maxrangner/nasta/components/display/matrix_animations.h

#pragma once

#include <stdint.h>

inline constexpr uint8_t kBoot1[64] = {
    1,0,0,0,0,0,0,0,
    0,0,0,0,0,0,0,0,
    0,0,0,0,0,0,0,0,
    0,0,0,0,0,0,0,0,
    0,0,0,0,0,0,0,0,
    0,0,0,0,0,0,0,0,
    0,0,0,0,0,0,0,0,
    0,0,0,0,0,0,0,0
};

inline constexpr uint8_t kBoot2[64] = {
    0,1,0,0,0,0,0,0,
    0,0,0,0,0,0,0,0,
    0,0,0,0,0,0,0,0,
    0,0,0,0,0,0,0,0,
    0,0,0,0,0,0,0,0,
    0,0,0,0,0,0,0,0,
    0,0,0,0,0,0,0,0,
    0,0,0,0,0,0,0,0
};

inline constexpr uint8_t kBoot3[64] = {
    0,0,1,0,0,0,0,0,
    0,0,0,0,0,0,0,0,
    0,0,0,0,0,0,0,0,
    0,0,0,0,0,0,0,0,
    0,0,0,0,0,0,0,0,
    0,0,0,0,0,0,0,0,
    0,0,0,0,0,0,0,0,
    0,0,0,0,0,0,0,0
};

inline constexpr uint8_t kBoot4[64] = {
    0,0,0,1,0,0,0,0,
    0,0,0,0,0,0,0,0,
    0,0,0,0,0,0,0,0,
    0,0,0,0,0,0,0,0,
    0,0,0,0,0,0,0,0,
    0,0,0,0,0,0,0,0,
    0,0,0,0,0,0,0,0,
    0,0,0,0,0,0,0,0
};

inline constexpr uint8_t kBoot5[64] = {
    0,0,0,0,1,0,0,0,
    0,0,0,0,0,0,0,0,
    0,0,0,0,0,0,0,0,
    0,0,0,0,0,0,0,0,
    0,0,0,0,0,0,0,0,
    0,0,0,0,0,0,0,0,
    0,0,0,0,0,0,0,0,
    0,0,0,0,0,0,0,0
};

inline constexpr uint8_t kBoot6[64] = {
    0,0,0,0,0,1,0,0,
    0,0,0,0,0,0,0,0,
    0,0,0,0,0,0,0,0,
    0,0,0,0,0,0,0,0,
    0,0,0,0,0,0,0,0,
    0,0,0,0,0,0,0,0,
    0,0,0,0,0,0,0,0,
    0,0,0,0,0,0,0,0
};

inline constexpr uint8_t kBoot7[64] = {
    0,0,0,0,0,0,1,0,
    0,0,0,0,0,0,0,0,
    0,0,0,0,0,0,0,0,
    0,0,0,0,0,0,0,0,
    0,0,0,0,0,0,0,0,
    0,0,0,0,0,0,0,0,
    0,0,0,0,0,0,0,0,
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
    kBoot61, kBoot62, kBoot63, kBoot64, kBoot65, kBoot66,
    kBoot67, kBoot68, kBoot69, kBoot70, kBoot71
};

inline constexpr const uint8_t* kWorkAnimation[] = {
    kWork1, kWork2, kWork3, kWork4
};

inline constexpr const uint8_t* kHeartAnimation[] = {
    kHeart1, kHeart2
};
