maxrangner/nasta/components/display/matrix_graphics.h

#pragma once

#include <stdint.h>

inline constexpr uint8_t kHeart[64] = {
    0,0,0,0,0,0,0,0,
    0,1,1,0,0,1,1,0,
    1,0,0,1,1,0,0,1,
    1,0,0,0,0,0,0,1,
    0,1,0,0,0,0,1,0,
    0,0,1,0,0,1,0,0,
    0,0,0,1,1,0,0,0,
    0,0,0,0,0,0,0,0
};

inline constexpr uint8_t kNum0[64] = {
    0,0,0,0,0,0,0,0,
    0,0,0,1,1,0,0,0,
    0,0,1,0,0,1,0,0,
    0,0,1,0,0,1,0,0,
    0,0,1,0,0,1,0,0,
    0,0,1,0,0,1,0,0,
    0,0,0,1,1,0,0,0,
    0,0,0,0,0,0,0,0
};

inline constexpr uint8_t kNum1[64] = {
    0,0,0,0,0,0,0,0,
    0,0,0,0,1,0,0,0,
    0,0,0,1,1,0,0,0,
    0,0,0,0,1,0,0,0,
    0,0,0,0,1,0,0,0,
    0,0,0,0,1,0,0,0,
    0,0,0,1,1,1,0,0,
    0,0,0,0,0,0,0,0
};

inline constexpr uint8_t kNum2[64] = {
    0,0,0,0,0,0,0,0,
    0,0,0,1,1,0,0,0,
    0,0,1,0,0,1,0,0,
    0,0,0,0,1,0,0,0,
    0,0,0,1,0,0,0,0,
    0,0,1,0,0,0,0,0,
    0,0,1,1,1,1,0,0,
    0,0,0,0,0,0,0,0
};

inline constexpr uint8_t kNum3[64] = {
    0,0,0,0,0,0,0,0,
    0,0,0,1,1,0,0,0,
    0,0,1,0,0,1,0,0,
    0,0,0,0,1,0,0,0,
    0,0,0,0,0,1,0,0,
    0,0,1,0,0,1,0,0,
    0,0,0,1,1,0,0,0,
    0,0,0,0,0,0,0,0
};

inline constexpr uint8_t kNum4[64] = {
    0,0,0,0,0,0,0,0,
    0,0,0,0,0,1,0,0,
    0,0,0,0,1,1,0,0,
    0,0,0,1,0,1,0,0,
    0,0,1,0,0,1,0,0,
    0,0,1,1,1,1,0,0,
    0,0,0,0,0,1,0,0,
    0,0,0,0,0,0,0,0
};

inline constexpr uint8_t kNum5[64] = {
    0,0,0,0,0,0,0,0,
    0,0,1,1,1,1,0,0,
    0,0,1,0,0,0,0,0,
    0,0,1,1,1,0,0,0,
    0,0,0,0,0,1,0,0,
    0,0,0,0,0,1,0,0,
    0,0,1,1,1,0,0,0,
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
    kNum0, kNum1, kNum2, kNum3, kNum4, kNum5, kNum6, kNum7, kNum8, kNum9,
    kNum10, kNum11, kNum12, kNum13, kNum14, kNum15, kNum16, kNum17, kNum18, kNum19,
    kNum20, kNum21, kNum22, kNum23, kNum24, kNum25, kNum26, kNum27, kNum28, kNum29, kNum30
};
